rbriski/solar_sensor/docs/images/plate-2.png

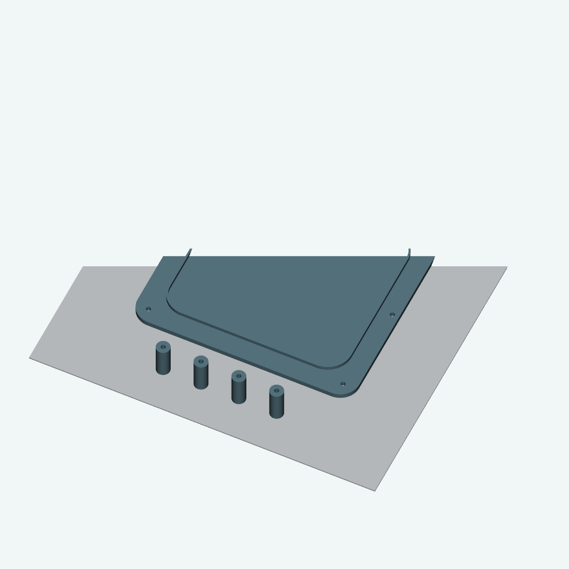
docs/images/plate-2.png
