rbriski/solar_sensor/hardware/enclosure/models/tray.step

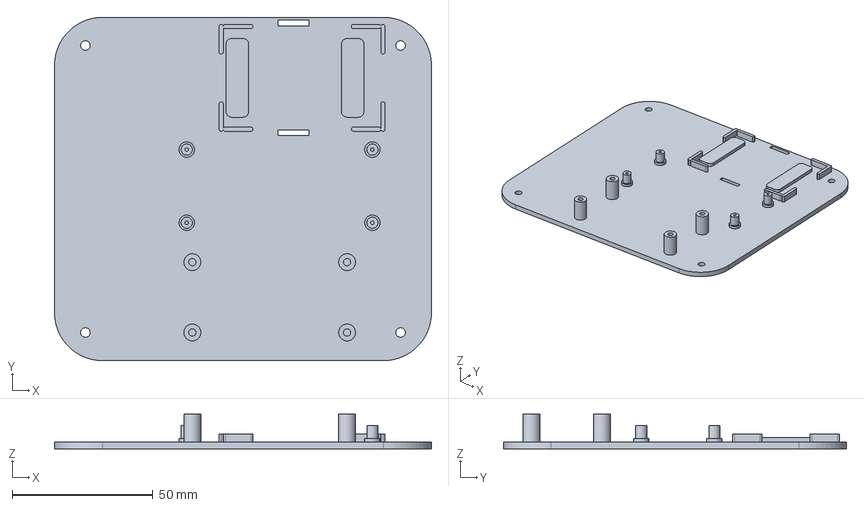
[picture p22: CAD file, 2026-10-08]
hardware/enclosure/models/tray.step
134.0 x 122.0 x 12.4 mm
