rbriski/solar_sensor/firmware/roof_sensor/ca_cert.h

// ISRG public roots from letsencrypt.org; server certificate verification stays enabled.
#pragma once
constexpr char ROOT_CA[] = R"CERT(-----BEGIN CERTIFICATE-----
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
-----END CERTIFICATE-----
-----BEGIN CERTIFICATE-----
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
/q4AaOeMSQ+2b1tbFfLn
-----END CERTIFICATE-----
)CERT";
